bwack/C64-Switchless-Multi-Kernal-27C256-adapter/KiCad_longboard/C64-Switchless_3D_fside.png

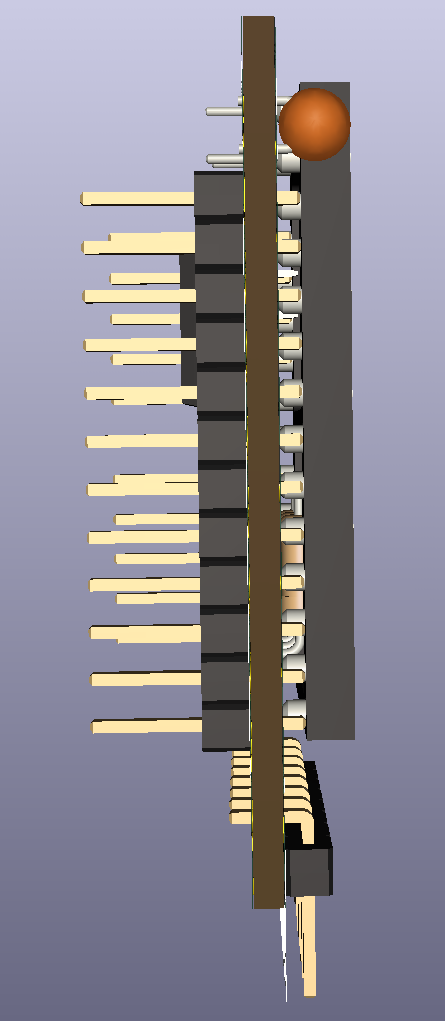
KiCad_longboard/C64-Switchless_3D_fside.png
