bwack/C64-Switchless-Multi-Kernal-27C256-adapter/KiCad_shortboard/C64-Switchless_3D_front.png

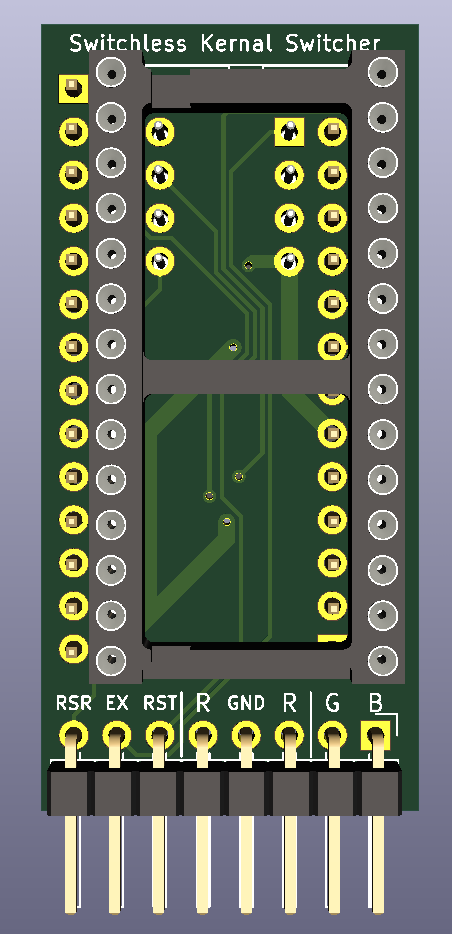
KiCad_shortboard/C64-Switchless_3D_front.png
