bwack/C64-Switchless-Multi-Kernal-27C256-adapter/User Guide/media/minipro.png

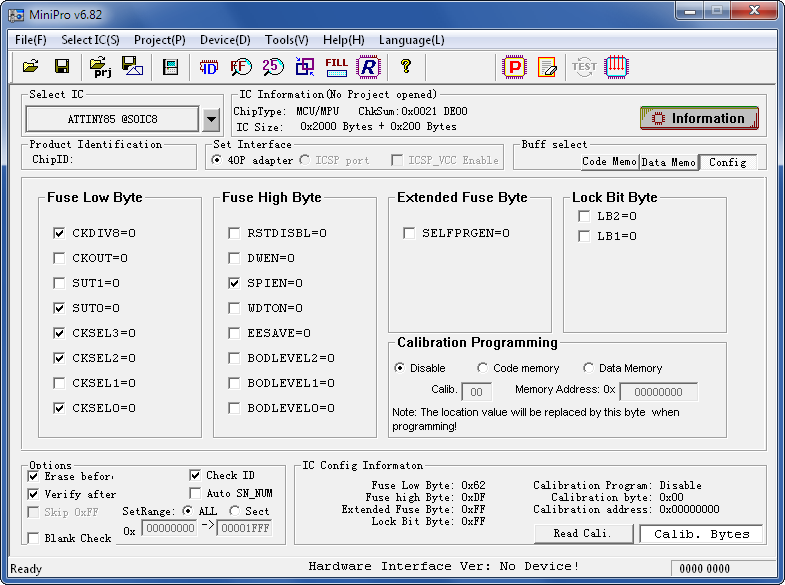
User Guide/media/minipro.png
